apuder/TRS-IO/doc/TRS-IO-M1-labels.png

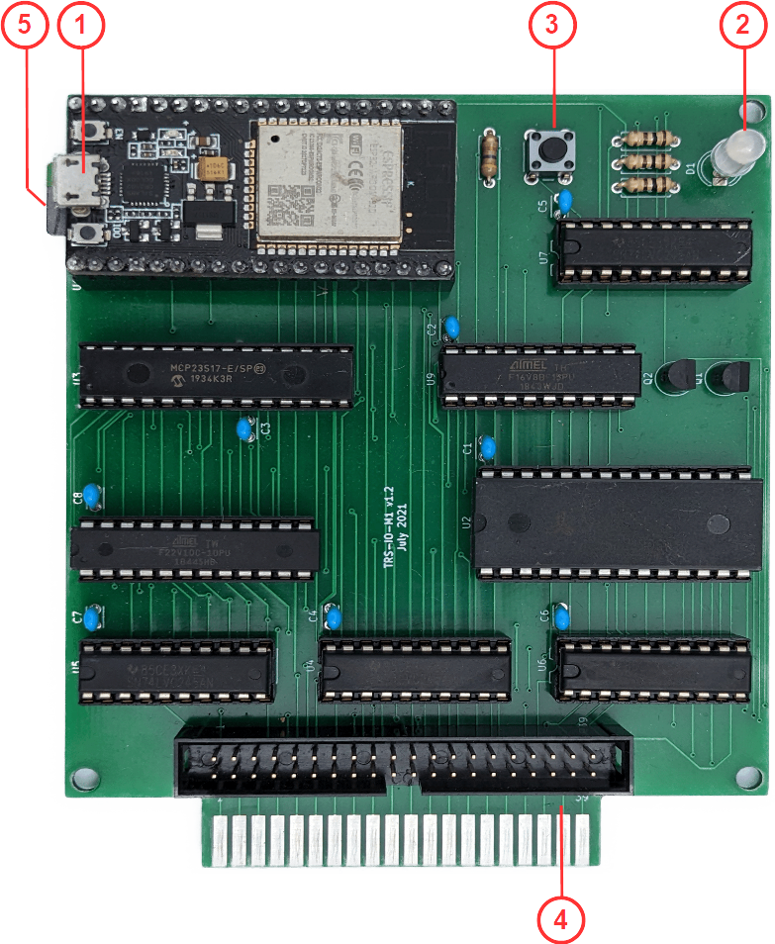
doc/TRS-IO-M1-labels.png
