apuder/TRS-IO/doc/TRS-IO-M1-v1_3.png

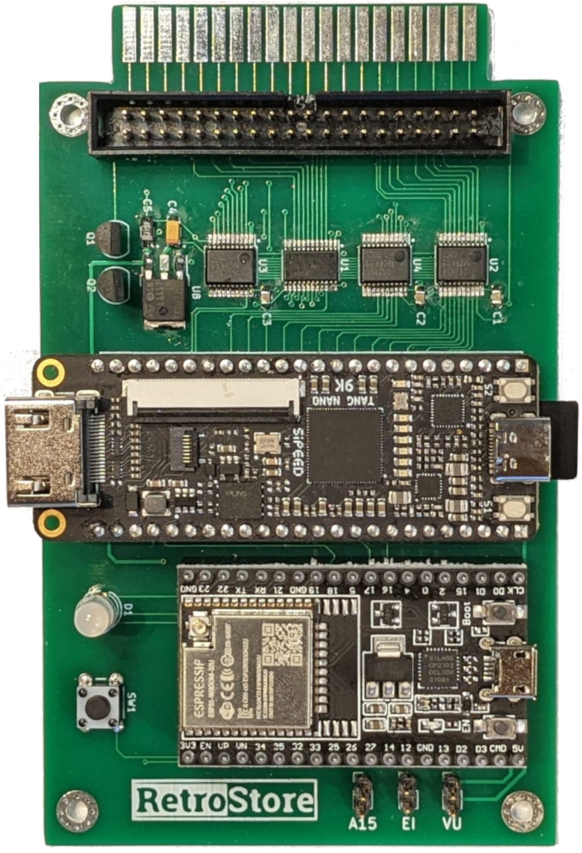
doc/TRS-IO-M1-v1_3.png
