apuder/TRS-IO/doc/TRS-IO-M1-XRAY.png

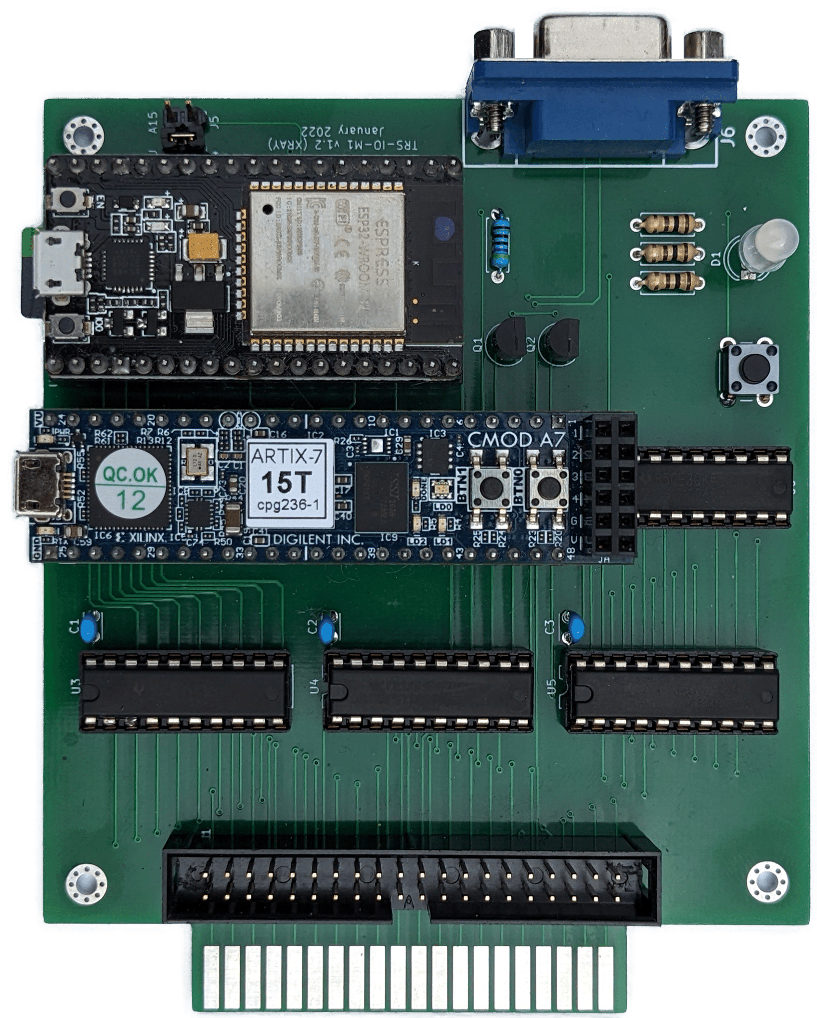
doc/TRS-IO-M1-XRAY.png
