apuder/TRS-IO/doc/TRS-IO-MIII-labels.png

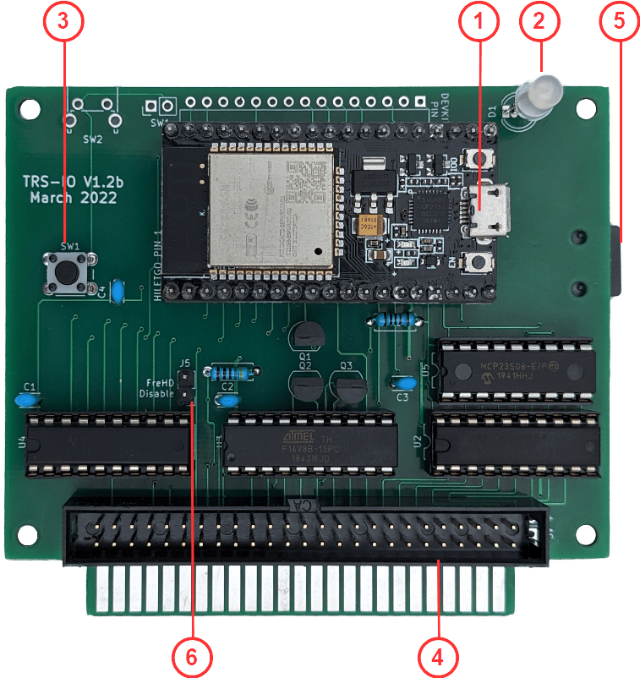
doc/TRS-IO-MIII-labels.png
