apuder/TRS-IO/doc/TRS-IO-MIII.png

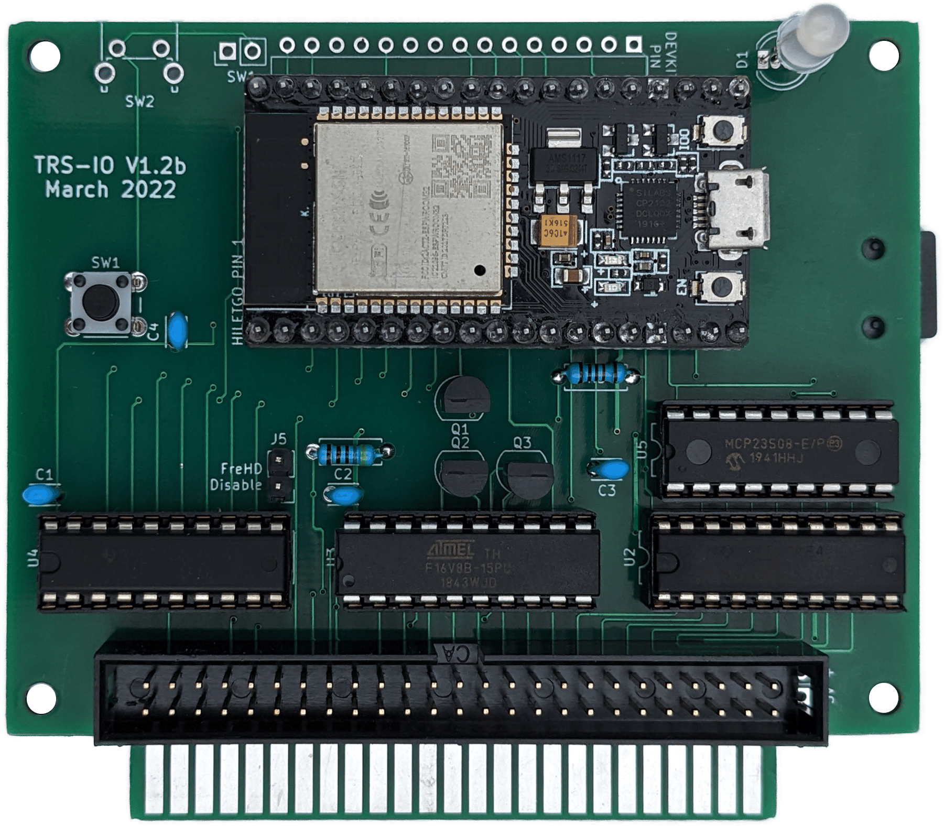
doc/TRS-IO-MIII.png
