apuder/TRS-IO/doc/trs-io-web-ui.png

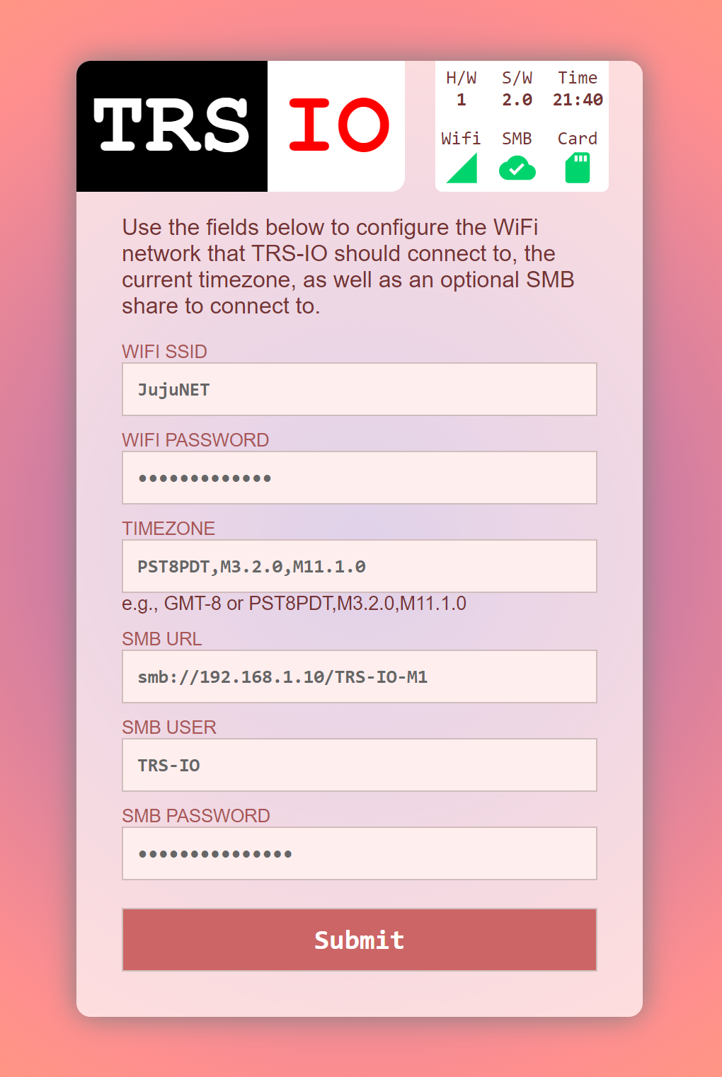
doc/trs-io-web-ui.png
