apuder/TRS-IO/src/images/help-guy.png

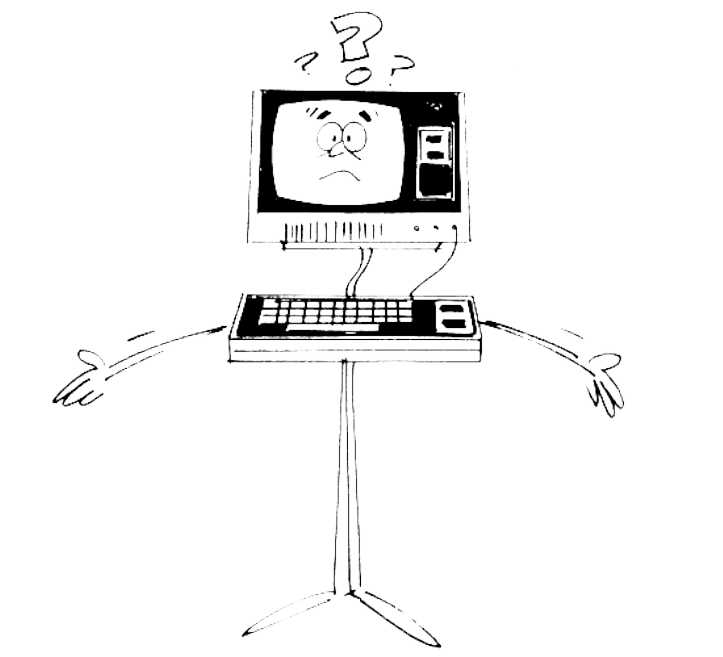
src/images/help-guy.png
