apuder/TRS-IO/src/fpga/pp/v1.1/ptrs-m1/src/gowin_sp/gowin_sp.v

//Copyright (C)2014-2022 Gowin Semiconductor Corporation.
//All rights reserved.
//File Title: IP file
//GOWIN Version: V1.9.8.09 Education
//Part Number: GW2A-LV18PG256C8/I7
//Device: GW2A-18C
//Created Time: Wed Apr 19 12:55:28 2023

module Gowin_SP_RAM (dout, clk, oce, ce, reset, wre, ad, din);

output [7:0] dout;
input clk;
input oce;
input ce;
input reset;
input wre;
input [15:0] ad;
input [7:0] din;

wire [30:0] sp_inst_0_dout_w;
wire [0:0] sp_inst_0_dout;
wire [30:0] sp_inst_1_dout_w;
wire [0:0] sp_inst_1_dout;
wire [30:0] sp_inst_2_dout_w;
wire [0:0] sp_inst_2_dout;
wire [30:0] sp_inst_3_dout_w;
wire [1:1] sp_inst_3_dout;
wire [30:0] sp_inst_4_dout_w;
wire [1:1] sp_inst_4_dout;
wire [30:0] sp_inst_5_dout_w;
wire [1:1] sp_inst_5_dout;
wire [30:0] sp_inst_6_dout_w;
wire [2:2] sp_inst_6_dout;
wire [30:0] sp_inst_7_dout_w;
wire [2:2] sp_inst_7_dout;
wire [30:0] sp_inst_8_dout_w;
wire [2:2] sp_inst_8_dout;
wire [30:0] sp_inst_9_dout_w;
wire [3:3] sp_inst_9_dout;
wire [30:0] sp_inst_10_dout_w;
wire [3:3] sp_inst_10_dout;
wire [30:0] sp_inst_11_dout_w;
wire [3:3] sp_inst_11_dout;
wire [30:0] sp_inst_12_dout_w;
wire [4:4] sp_inst_12_dout;
wire [30:0] sp_inst_13_dout_w;
wire [4:4] sp_inst_13_dout;
wire [30:0] sp_inst_14_dout_w;
wire [4:4] sp_inst_14_dout;
wire [30:0] sp_inst_15_dout_w;
wire [5:5] sp_inst_15_dout;
wire [30:0] sp_inst_16_dout_w;
wire [5:5] sp_inst_16_dout;
wire [30:0] sp_inst_17_dout_w;
wire [5:5] sp_inst_17_dout;
wire [30:0] sp_inst_18_dout_w;
wire [6:6] sp_inst_18_dout;
wire [30:0] sp_inst_19_dout_w;
wire [6:6] sp_inst_19_dout;
wire [30:0] sp_inst_20_dout_w;
wire [6:6] sp_inst_20_dout;
wire [30:0] sp_inst_21_dout_w;
wire [7:7] sp_inst_21_dout;
wire [30:0] sp_inst_22_dout_w;
wire [7:7] sp_inst_22_dout;
wire [30:0] sp_inst_23_dout_w;
wire [7:7] sp_inst_23_dout;
wire dff_q_0;
wire dff_q_1;
wire mux_o_0;
wire mux_o_3;
wire mux_o_6;
wire mux_o_9;
wire mux_o_12;
wire mux_o_15;
wire mux_o_18;
wire mux_o_21;
wire ce_w;
wire gw_gnd;

assign ce_w = ~wre & ce;
assign gw_gnd = 1'b0;

SP sp_inst_0 (
    .DO({sp_inst_0_dout_w[30:0],sp_inst_0_dout[0]}),
    .CLK(clk),
    .OCE(oce),
    .CE(ce),
    .RESET(reset),
    .WRE(wre),
    .BLKSEL({gw_gnd,ad[15],ad[14]}),
    .AD(ad[13:0]),
    .DI({gw_gnd,gw_gnd,gw_gnd,gw_gnd,gw_gnd,gw_gnd,gw_gnd,gw_gnd,gw_gnd,gw_gnd,gw_gnd,gw_gnd,gw_gnd,gw_gnd,gw_gnd,gw_gnd,gw_gnd,gw_gnd,gw_gnd,gw_gnd,gw_gnd,gw_gnd,gw_gnd,gw_gnd,gw_gnd,gw_gnd,gw_gnd,gw_gnd,gw_gnd,gw_gnd,gw_gnd,din[0]})
);

defparam sp_inst_0.READ_MODE = 1'b0;
defparam sp_inst_0.WRITE_MODE = 2'b00;
defparam sp_inst_0.BIT_WIDTH = 1;
defparam sp_inst_0.BLK_SEL = 3'b000;
defparam sp_inst_0.RESET_MODE = "SYNC";
defparam sp_inst_0.INIT_RAM_00 = 256'h0000000000000000000000000000000000000000000000000000000000000000;
defparam sp_inst_0.INIT_RAM_01 = 256'h0000000000000000000000000000000000000000000000000000000000000000;
defparam sp_inst_0.INIT_RAM_02 = 256'h0000000000000000000000000000000000000000000000000000000000000000;
defparam sp_inst_0.INIT_RAM_03 = 256'h0000000000000000000000000000000000000000000000000000000000000000;
defparam sp_inst_0.INIT_RAM_04 = 256'h0000000000000000000000000000000000000000000000000000000000000000;
defparam sp_inst_0.INIT_RAM_05 = 256'h0000000000000000000000000000000000000000000000000000000000000000;
defparam sp_inst_0.INIT_RAM_06 = 256'h0000000000000000000000000000000000000000000000000000000000000000;
defparam sp_inst_0.INIT_RAM_07 = 256'h0000000000000000000000000000000000000000000000000000000000000000;
defparam sp_inst_0.INIT_RAM_08 = 256'h0000000000000000000000000000000000000000000000000000000000000000;
defparam sp_inst_0.INIT_RAM_09 = 256'h0000000000000000000000000000000000000000000000000000000000000000;
defparam sp_inst_0.INIT_RAM_0A = 256'h0000000000000000000000000000000000000000000000000000000000000000;
defparam sp_inst_0.INIT_RAM_0B = 256'h0000000000000000000000000000000000000000000000000000000000000000;
defparam sp_inst_0.INIT_RAM_0C = 256'h0000000000000000000000000000000000000000000000000000000000000000;
defparam sp_inst_0.INIT_RAM_0D = 256'h0000000000000000000000000000000000000000000000000000000000000000;
defparam sp_inst_0.INIT_RAM_0E = 256'h0000000000000000000000000000000000000000000000000000000000000000;
defparam sp_inst_0.INIT_RAM_0F = 256'h0000000000000000000000000000000000000000000000000000000000000000;
defparam sp_inst_0.INIT_RAM_10 = 256'h0000000000000000000000000000000000000000000000000000000000000000;
defparam sp_inst_0.INIT_RAM_11 = 256'h0000000000000000000000000000000000000000000000000000000000000000;
defparam sp_inst_0.INIT_RAM_12 = 256'h0000040000000000000000008000000000000001224ECED4B4DDBABB9CC04820;
defparam sp_inst_0.INIT_RAM_13 = 256'h1008000001C00380000000000000000000000000000000000000000000000000;
defparam sp_inst_0.INIT_RAM_14 = 256'h0000000000000000000000000000000000000000000000000000000E00000000;
defparam sp_inst_0.INIT_RAM_15 = 256'h0000000000000000000000000000000000000000000000000000000000000000;
defparam sp_inst_0.INIT_RAM_16 = 256'h0000000000000000000000000000000000000000000000000000000000000000;
defparam sp_inst_0.INIT_RAM_17 = 256'h0000000000000000000000000000000000000000000000000000000000000000;
defparam sp_inst_0.INIT_RAM_18 = 256'h00000000000000000000000000000000000000000EBF39B3573D5EF44D989997;
defparam sp_inst_0.INIT_RAM_19 = 256'h0000000000000000000000000000000000000000000000000000000000000000;
defparam sp_inst_0.INIT_RAM_1A = 256'h0000000000000000000000000000000000000000000000000000000000000000;
defparam sp_inst_0.INIT_RAM_1B = 256'h0000000000000000000000000000000000000000000000000000000000000000;
defparam sp_inst_0.INIT_RAM_1C = 256'h0000000000000000000000000000000000000000000000000000000000000000;
defparam sp_inst_0.INIT_RAM_1D = 256'h0000000000000000000000000000000000000000000000000000000000000000;
defparam sp_inst_0.INIT_RAM_1E = 256'h0000000000000000000000000000000000000000000000000000000000000000;
defparam sp_inst_0.INIT_RAM_1F = 256'h0000000000000000000000000000000000000000000000000000000000000000;
defparam sp_inst_0.INIT_RAM_20 = 256'h0000000000000000000000000000000000000000000000000000000000000000;
defparam sp_inst_0.INIT_RAM_21 = 256'h0000000000000000000000000000000000000000000000000000000000000000;
defparam sp_inst_0.INIT_RAM_22 = 256'h0000000000000000000000000000000000000000000000000000000000000000;
defparam sp_inst_0.INIT_RAM_23 = 256'h0000000000000000000000000000000000000000000000000000000000000000;
defparam sp_inst_0.INIT_RAM_24 = 256'h0000000000000000000000000000000000000000000000000000000000000000;
defparam sp_inst_0.INIT_RAM_25 = 256'h0000000000000000000000000000000000000000000000000000000000000000;
defparam sp_inst_0.INIT_RAM_26 = 256'h0000000000000000000000000000000000000000000000000000000000000000;
defparam sp_inst_0.INIT_RAM_27 = 256'h0000000000000000000000000000000000000000000000000000000000000000;
defparam sp_inst_0.INIT_RAM_28 = 256'h0000000000000000000000000000000000000000000000000000000000000000;
defparam sp_inst_0.INIT_RAM_29 = 256'h0000000000000000000000000000000000000000000000000000000000000000;
defparam sp_inst_0.INIT_RAM_2A = 256'h0000000000000000000000000000000000000000000000000000000000000000;
defparam sp_inst_0.INIT_RAM_2B = 256'h0000000000000000000000000000000000000000000000000000000000000000;
defparam sp_inst_0.INIT_RAM_2C = 256'h0000000000000000000000000000000000000000000000000000000000000000;
defparam sp_inst_0.INIT_RAM_2D = 256'h0000000000000000000000000000000000000000000000000000000000000000;
defparam sp_inst_0.INIT_RAM_2E = 256'h0000000000000000000000000000000000000000000000000000000000000000;
defparam sp_inst_0.INIT_RAM_2F = 256'h0000000000000000000000000000000000000000000000000000000000000000;
defparam sp_inst_0.INIT_RAM_30 = 256'h0000000000000000000000000000000000000000000000000000000000000000;
defparam sp_inst_0.INIT_RAM_31 = 256'h0000000000000000000000000000000000000000000000000000000000000000;
defparam sp_inst_0.INIT_RAM_32 = 256'h0000000000000000000000000000000000000000000000000000000000000000;
defparam sp_inst_0.INIT_RAM_33 = 256'h0000000000000000000000000000000000000000000000000000000000000000;
defparam sp_inst_0.INIT_RAM_34 = 256'h0000000000000000000000000000000000000000000000000000000000000000;
defparam sp_inst_0.INIT_RAM_35 = 256'h0000000000000000000000000000000000000000000000000000000000000000;
defparam sp_inst_0.INIT_RAM_36 = 256'h0000000000000000000000000000000000000000000000000000000000000000;
defparam sp_inst_0.INIT_RAM_37 = 256'h0000000000000000000000000000000000000000000000000000000000000000;
defparam sp_inst_0.INIT_RAM_38 = 256'h0000000000000000000000000000000000000000000000000000000000000000;
defparam sp_inst_0.INIT_RAM_39 = 256'h0000000000000000000000000000000000000000000000000000000000000000;
defparam sp_inst_0.INIT_RAM_3A = 256'h0000000000000000000000000000000000000000000000000000000000000000;
defparam sp_inst_0.INIT_RAM_3B = 256'h0000000000000000000000000000000000000000000000000000000000000000;
defparam sp_inst_0.INIT_RAM_3C = 256'h0000000000000000000000000000000000000000000000000000000000000000;
defparam sp_inst_0.INIT_RAM_3D = 256'h0000000000000000000000000000000000000000000000000000000000000000;
defparam sp_inst_0.INIT_RAM_3E = 256'h0000000000000000000000000000000000000000000000000000000000000000;
defparam sp_inst_0.INIT_RAM_3F = 256'h0000000000000000000000000000000000000000000000000000000000000000;

SP sp_inst_1 (
    .DO({sp_inst_1_dout_w[30:0],sp_inst_1_dout[0]}),
    .CLK(clk),
    .OCE(oce),
    .CE(ce),
    .RESET(reset),
    .WRE(wre),
    .BLKSEL({gw_gnd,ad[15],ad[14]}),
    .AD(ad[13:0]),
    .DI({gw_gnd,gw_gnd,gw_gnd,gw_gnd,gw_gnd,gw_gnd,gw_gnd,gw_gnd,gw_gnd,gw_gnd,gw_gnd,gw_gnd,gw_gnd,gw_gnd,gw_gnd,gw_gnd,gw_gnd,gw_gnd,gw_gnd,gw_gnd,gw_gnd,gw_gnd,gw_gnd,gw_gnd,gw_gnd,gw_gnd,gw_gnd,gw_gnd,gw_gnd,gw_gnd,gw_gnd,din[0]})
);

defparam sp_inst_1.READ_MODE = 1'b0;
defparam sp_inst_1.WRITE_MODE = 2'b00;
defparam sp_inst_1.BIT_WIDTH = 1;
defparam sp_inst_1.BLK_SEL = 3'b001;
defparam sp_inst_1.RESET_MODE = "SYNC";
defparam sp_inst_1.INIT_RAM_00 = 256'h0000000000000000000000000000000000000000000000000000000000000000;
defparam sp_inst_1.INIT_RAM_01 = 256'h0000000000000000000000000000000000000000000000000000000000000000;
defparam sp_inst_1.INIT_RAM_02 = 256'h0000000000000000000000000000000000000000000000000000000000000000;
defparam sp_inst_1.INIT_RAM_03 = 256'h0000000000000000000000000000000000000000000000000000000000000000;
defparam sp_inst_1.INIT_RAM_04 = 256'h0000000000000000000000000000000000000000000000000000000000000000;
defparam sp_inst_1.INIT_RAM_05 = 256'h0000000000000000000000000000000000000000000000000000000000000000;
defparam sp_inst_1.INIT_RAM_06 = 256'h0000000000000000000000000000000000000000000000000000000000000000;
defparam sp_inst_1.INIT_RAM_07 = 256'h0000000000000000000000000000000000000000000000000000000000000000;
defparam sp_inst_1.INIT_RAM_08 = 256'h0000000000000000000000000000000000000000000000000000000000000000;
defparam sp_inst_1.INIT_RAM_09 = 256'h0000000000000000000000000000000000000000000000000000000000000000;
defparam sp_inst_1.INIT_RAM_0A = 256'h0000000000000000000000000000000000000000000000000000000000000000;
defparam sp_inst_1.INIT_RAM_0B = 256'h0000000000000000000000000000000000000000000000000000000000000000;
defparam sp_inst_1.INIT_RAM_0C = 256'h0000000000000000000000000000000000000000000000000000000000000000;
defparam sp_inst_1.INIT_RAM_0D = 256'h0000000000000000000000000000000000000000000000000000000000000000;
defparam sp_inst_1.INIT_RAM_0E = 256'h0000000000000000000000000000000000000000000000000000000000000000;
defparam sp_inst_1.INIT_RAM_0F = 256'h0000000000000000000000000000000000000000000000000000000000000000;
defparam sp_inst_1.INIT_RAM_10 = 256'h0000000000000000000000000000000000000000000000000000000000000000;
defparam sp_inst_1.INIT_RAM_11 = 256'h0000000000000000000000000000000000000000000000000000000000000000;
defparam sp_inst_1.INIT_RAM_12 = 256'h0000000000000000000000000000000000000000000000000000000000000000;
defparam sp_inst_1.INIT_RAM_13 = 256'h0000000000000000000000000000000000000000000000000000000000000000;
defparam sp_inst_1.INIT_RAM_14 = 256'h0000000000000000000000000000000000000000000000000000000000000000;
defparam sp_inst_1.INIT_RAM_15 = 256'h0000000000000000000000000000000000000000000000000000000000000000;
defparam sp_inst_1.INIT_RAM_16 = 256'h0000000000000000000000000000000000000000000000000000000000000000;
defparam sp_inst_1.INIT_RAM_17 = 256'h0000000000000000000000000000000000000000000000000000000000000000;
defparam sp_inst_1.INIT_RAM_18 = 256'h0000000000000000000000000000000000000000000000000000000000000000;
defparam sp_inst_1.INIT_RAM_19 = 256'h0000000000000000000000000000000000000000000000000000000000000000;
defparam sp_inst_1.INIT_RAM_1A = 256'h0000000000000000000000000000000000000000000000000000000000000000;
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
defparam sp_inst_2.INIT_RAM_35 = 256'h0000000000000000000000000000000000000000000000000000000000000000;
defparam sp_inst_2.INIT_RAM_36 = 256'h0000000000000000000000000000000000000000000000000000000000000000;
defparam sp_inst_2.INIT_RAM_37 = 256'h0000000000000000000000000000000000000000000000000000000000000000;
defparam sp_inst_2.INIT_RAM_38 = 256'h0000000000000000000000000000000000000000000000000000000000000000;
defparam sp_inst_2.INIT_RAM_39 = 256'h0000000000000000000000000000000000000000000000000000000000000000;
defparam sp_inst_2.INIT_RAM_3A = 256'h0000000000000000000000000000000000000000000000000000000000000000;
defparam sp_inst_2.INIT_RAM_3B = 256'h0000000000000000000000000000000000000000000000000000000000000000;
defparam sp_inst_2.INIT_RAM_3C = 256'h0000000000000000000000000000000000000000000000000000000000000000;
defparam sp_inst_2.INIT_RAM_3D = 256'h0000000000000000000000000000000000000000000000000000000000000000;
defparam sp_inst_2.INIT_RAM_3E = 256'h0000000000000000000000000000000000000000000000000000000000000000;
defparam sp_inst_2.INIT_RAM_3F = 256'h0000000000000000000000000000000000000000000000000000000000000000;

SP sp_inst_3 (
    .DO({sp_inst_3_dout_w[30:0],sp_inst_3_dout[1]}),
    .CLK(clk),
    .OCE(oce),
    .CE(ce),
    .RESET(reset),
    .WRE(wre),
    .BLKSEL({gw_gnd,ad[15],ad[14]}),
    .AD(ad[13:0]),
    .DI({gw_gnd,gw_gnd,gw_gnd,gw_gnd,gw_gnd,gw_gnd,gw_gnd,gw_gnd,gw_gnd,gw_gnd,gw_gnd,gw_gnd,gw_gnd,gw_gnd,gw_gnd,gw_gnd,gw_gnd,gw_gnd,gw_gnd,gw_gnd,gw_gnd,gw_gnd,gw_gnd,gw_gnd,gw_gnd,gw_gnd,gw_gnd,gw_gnd,gw_gnd,gw_gnd,gw_gnd,din[1]})
);

defparam sp_inst_3.READ_MODE = 1'b0;
defparam sp_inst_3.WRITE_MODE = 2'b00;
defparam sp_inst_3.BIT_WIDTH = 1;
defparam sp_inst_3.BLK_SEL = 3'b000;
defparam sp_inst_3.RESET_MODE = "SYNC";
defparam sp_inst_3.INIT_RAM_00 = 256'h0000000000000000000000000000000000000000000000000000000000000000;
defparam sp_inst_3.INIT_RAM_01 = 256'h0000000000000000000000000000000000000000000000000000000000000000;
defparam sp_inst_3.INIT_RAM_02 = 256'h0000000000000000000000000000000000000000000000000000000000000000;
defparam sp_inst_3.INIT_RAM_03 = 256'h0000000000000000000000000000000000000000000000000000000000000000;
defparam sp_inst_3.INIT_RAM_04 = 256'h0000000000000000000000000000000000000000000000000000000000000000;
defparam sp_inst_3.INIT_RAM_05 = 256'h0000000000000000000000000000000000000000000000000000000000000000;
defparam sp_inst_3.INIT_RAM_06 = 256'h0000000000000000000000000000000000000000000000000000000000000000;
defparam sp_inst_3.INIT_RAM_07 = 256'h0000000000000000000000000000000000000000000000000000000000000000;
defparam sp_inst_3.INIT_RAM_08 = 256'h0000000000000000000000000000000000000000000000000000000000000000;
defparam sp_inst_3.INIT_RAM_09 = 256'h0000000000000000000000000000000000000000000000000000000000000000;
defparam sp_inst_3.INIT_RAM_0A = 256'h0000000000000000000000000000000000000000000000000000000000000000;
defparam sp_inst_3.INIT_RAM_0B = 256'h0000000000000000000000000000000000000000000000000000000000000000;
defparam sp_inst_3.INIT_RAM_0C = 256'h0000000000000000000000000000000000000000000000000000000000000000;
defparam sp_inst_3.INIT_RAM_0D = 256'h0000000000000000000000000000000000000000000000000000000000000000;
defparam sp_inst_3.INIT_RAM_0E = 256'h0000000000000000000000000000000000000000000000000000000000000000;
defparam sp_inst_3.INIT_RAM_0F = 256'h0000000000000000000000000000000000000000000000000000000000000000;
defparam sp_inst_3.INIT_RAM_10 = 256'h0000000000000000000000000000000000000000000000000000000000000000;
defparam sp_inst_3.INIT_RAM_11 = 256'h0000000000000000000000000000000000000000000000000000000000000000;
defparam sp_inst_3.INIT_RAM_12 = 256'h04040806705CE43BEE700C010082402D822804001202004C3C442E0631A620F7;
defparam sp_inst_3.INIT_RAM_13 = 256'h300BA357262E8C08EB39BE07C00213E48C48E23A360BA31FC5CE8F83F7B9F171;
defparam sp_inst_3.INIT_RAM_14 = 256'h000000000000000000000000000000000000000000000002802223F08A89643C;
defparam sp_inst_3.INIT_RAM_15 = 256'h0000000000000000000000000000000000000000000000000000000000000000;
defparam sp_inst_3.INIT_RAM_16 = 256'h0000000000000000000000000000000000000000000000000000000000000000;
defparam sp_inst_3.INIT_RAM_17 = 256'h0000000000000000000000000000000000000000000000000000000000000000;
defparam sp_inst_3.INIT_RAM_18 = 256'h000000000000000000000000000000000000000000288088C0C62A05682D8000;
defparam sp_inst_3.INIT_RAM_19 = 256'h0000000000000000000000000000000000000000000000000000000000000000;
defparam sp_inst_3.INIT_RAM_1A = 256'h0000000000000000000000000000000000000000000000000000000000000000;
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
defparam sp_inst_4.INIT_RAM_35 = 256'h0000000000000000000000000000000000000000000000000000000000000000;
defparam sp_inst_4.INIT_RAM_36 = 256'h0000000000000000000000000000000000000000000000000000000000000000;
defparam sp_inst_4.INIT_RAM_37 = 256'h0000000000000000000000000000000000000000000000000000000000000000;
defparam sp_inst_4.INIT_RAM_38 = 256'h0000000000000000000000000000000000000000000000000000000000000000;
defparam sp_inst_4.INIT_RAM_39 = 256'h0000000000000000000000000000000000000000000000000000000000000000;
defparam sp_inst_4.INIT_RAM_3A = 256'h0000000000000000000000000000000000000000000000000000000000000000;
defparam sp_inst_4.INIT_RAM_3B = 256'h0000000000000000000000000000000000000000000000000000000000000000;
defparam sp_inst_4.INIT_RAM_3C = 256'h0000000000000000000000000000000000000000000000000000000000000000;
defparam sp_inst_4.INIT_RAM_3D = 256'h0000000000000000000000000000000000000000000000000000000000000000;
defparam sp_inst_4.INIT_RAM_3E = 256'h0000000000000000000000000000000000000000000000000000000000000000;
defparam sp_inst_4.INIT_RAM_3F = 256'h0000000000000000000000000000000000000000000000000000000000000000;

SP sp_inst_5 (
    .DO({sp_inst_5_dout_w[30:0],sp_inst_5_dout[1]}),
    .CLK(clk),
    .OCE(oce),
    .CE(ce),
    .RESET(reset),
    .WRE(wre),
    .BLKSEL({gw_gnd,ad[15],ad[14]}),
    .AD(ad[13:0]),
    .DI({gw_gnd,gw_gnd,gw_gnd,gw_gnd,gw_gnd,gw_gnd,gw_gnd,gw_gnd,gw_gnd,gw_gnd,gw_gnd,gw_gnd,gw_gnd,gw_gnd,gw_gnd,gw_gnd,gw_gnd,gw_gnd,gw_gnd,gw_gnd,gw_gnd,gw_gnd,gw_gnd,gw_gnd,gw_gnd,gw_gnd,gw_gnd,gw_gnd,gw_gnd,gw_gnd,gw_gnd,din[1]})
);

defparam sp_inst_5.READ_MODE = 1'b0;
defparam sp_inst_5.WRITE_MODE = 2'b00;
defparam sp_inst_5.BIT_WIDTH = 1;
defparam sp_inst_5.BLK_SEL = 3'b010;
defparam sp_inst_5.RESET_MODE = "SYNC";
defparam sp_inst_5.INIT_RAM_00 = 256'h0000000000000000000000000000000000000000000000000000000000000000;
defparam sp_inst_5.INIT_RAM_01 = 256'h0000000000000000000000000000000000000000000000000000000000000000;
defparam sp_inst_5.INIT_RAM_02 = 256'h0000000000000000000000000000000000000000000000000000000000000000;
defparam sp_inst_5.INIT_RAM_03 = 256'h0000000000000000000000000000000000000000000000000000000000000000;
defparam sp_inst_5.INIT_RAM_04 = 256'h0000000000000000000000000000000000000000000000000000000000000000;
defparam sp_inst_5.INIT_RAM_05 = 256'h0000000000000000000000000000000000000000000000000000000000000000;
defparam sp_inst_5.INIT_RAM_06 = 256'h0000000000000000000000000000000000000000000000000000000000000000;
defparam sp_inst_5.INIT_RAM_07 = 256'h0000000000000000000000000000000000000000000000000000000000000000;
defparam sp_inst_5.INIT_RAM_08 = 256'h0000000000000000000000000000000000000000000000000000000000000000;
defparam sp_inst_5.INIT_RAM_09 = 256'h0000000000000000000000000000000000000000000000000000000000000000;
defparam sp_inst_5.INIT_RAM_0A = 256'h0000000000000000000000000000000000000000000000000000000000000000;
defparam sp_inst_5.INIT_RAM_0B = 256'h0000000000000000000000000000000000000000000000000000000000000000;
defparam sp_inst_5.INIT_RAM_0C = 256'h0000000000000000000000000000000000000000000000000000000000000000;
defparam sp_inst_5.INIT_RAM_0D = 256'h0000000000000000000000000000000000000000000000000000000000000000;
defparam sp_inst_5.INIT_RAM_0E = 256'h0000000000000000000000000000000000000000000000000000000000000000;
defparam sp_inst_5.INIT_RAM_0F = 256'h0000000000000000000000000000000000000000000000000000000000000000;
defparam sp_inst_5.INIT_RAM_10 = 256'h0000000000000000000000000000000000000000000000000000000000000000;
defparam sp_inst_5.INIT_RAM_11 = 256'h0000000000000000000000000000000000000000000000000000000000000000;
defparam sp_inst_5.INIT_RAM_12 = 256'h0000000000000000000000000000000000000000000000000000000000000000;
defparam sp_inst_5.INIT_RAM_13 = 256'h0000000000000000000000000000000000000000000000000000000000000000;
defparam sp_inst_5.INIT_RAM_14 = 256'h0000000000000000000000000000000000000000000000000000000000000000;
defparam sp_inst_5.INIT_RAM_15 = 256'h0000000000000000000000000000000000000000000000000000000000000000;
defparam sp_inst_5.INIT_RAM_16 = 256'h0000000000000000000000000000000000000000000000000000000000000000;
defparam sp_inst_5.INIT_RAM_17 = 256'h0000000000000000000000000000000000000000000000000000000000000000;
defparam sp_inst_5.INIT_RAM_18 = 256'h0000000000000000000000000000000000000000000000000000000000000000;
defparam sp_inst_5.INIT_RAM_19 = 256'h0000000000000000000000000000000000000000000000000000000000000000;
defparam sp_inst_5.INIT_RAM_1A = 256'h0000000000000000000000000000000000000000000000000000000000000000;
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
defparam sp_inst_6.INIT_RAM_35 = 256'h0000000000000000000000000000000000000000000000000000000000000000;
defparam sp_inst_6.INIT_RAM_36 = 256'h0000000000000000000000000000000000000000000000000000000000000000;
defparam sp_inst_6.INIT_RAM_37 = 256'h0000000000000000000000000000000000000000000000000000000000000000;
defparam sp_inst_6.INIT_RAM_38 = 256'h0000000000000000000000000000000000000000000000000000000000000000;
defparam sp_inst_6.INIT_RAM_39 = 256'h0000000000000000000000000000000000000000000000000000000000000000;
defparam sp_inst_6.INIT_RAM_3A = 256'h0000000000000000000000000000000000000000000000000000000000000000;
defparam sp_inst_6.INIT_RAM_3B = 256'h0000000000000000000000000000000000000000000000000000000000000000;
defparam sp_inst_6.INIT_RAM_3C = 256'h0000000000000000000000000000000000000000000000000000000000000000;
defparam sp_inst_6.INIT_RAM_3D = 256'h0000000000000000000000000000000000000000000000000000000000000000;
defparam sp_inst_6.INIT_RAM_3E = 256'h0000000000000000000000000000000000000000000000000000000000000000;
defparam sp_inst_6.INIT_RAM_3F = 256'h0000000000000000000000000000000000000000000000000000000000000000;

SP sp_inst_7 (
    .DO({sp_inst_7_dout_w[30:0],sp_inst_7_dout[2]}),
    .CLK(clk),
    .OCE(oce),
    .CE(ce),
    .RESET(reset),
    .WRE(wre),
    .BLKSEL({gw_gnd,ad[15],ad[14]}),
    .AD(ad[13:0]),
    .DI({gw_gnd,gw_gnd,gw_gnd,gw_gnd,gw_gnd,gw_gnd,gw_gnd,gw_gnd,gw_gnd,gw_gnd,gw_gnd,gw_gnd,gw_gnd,gw_gnd,gw_gnd,gw_gnd,gw_gnd,gw_gnd,gw_gnd,gw_gnd,gw_gnd,gw_gnd,gw_gnd,gw_gnd,gw_gnd,gw_gnd,gw_gnd,gw_gnd,gw_gnd,gw_gnd,gw_gnd,din[2]})
);

defparam sp_inst_7.READ_MODE = 1'b0;
defparam sp_inst_7.WRITE_MODE = 2'b00;
defparam sp_inst_7.BIT_WIDTH = 1;
defparam sp_inst_7.BLK_SEL = 3'b001;
defparam sp_inst_7.RESET_MODE = "SYNC";
defparam sp_inst_7.INIT_RAM_00 = 256'h0000000000000000000000000000000000000000000000000000000000000000;
defparam sp_inst_7.INIT_RAM_01 = 256'h0000000000000000000000000000000000000000000000000000000000000000;
defparam sp_inst_7.INIT_RAM_02 = 256'h0000000000000000000000000000000000000000000000000000000000000000;
defparam sp_inst_7.INIT_RAM_03 = 256'h0000000000000000000000000000000000000000000000000000000000000000;
defparam sp_inst_7.INIT_RAM_04 = 256'h0000000000000000000000000000000000000000000000000000000000000000;
defparam sp_inst_7.INIT_RAM_05 = 256'h0000000000000000000000000000000000000000000000000000000000000000;
defparam sp_inst_7.INIT_RAM_06 = 256'h0000000000000000000000000000000000000000000000000000000000000000;
defparam sp_inst_7.INIT_RAM_07 = 256'h0000000000000000000000000000000000000000000000000000000000000000;
defparam sp_inst_7.INIT_RAM_08 = 256'h0000000000000000000000000000000000000000000000000000000000000000;
defparam sp_inst_7.INIT_RAM_09 = 256'h0000000000000000000000000000000000000000000000000000000000000000;
defparam sp_inst_7.INIT_RAM_0A = 256'h0000000000000000000000000000000000000000000000000000000000000000;
defparam sp_inst_7.INIT_RAM_0B = 256'h0000000000000000000000000000000000000000000000000000000000000000;
defparam sp_inst_7.INIT_RAM_0C = 256'h0000000000000000000000000000000000000000000000000000000000000000;
defparam sp_inst_7.INIT_RAM_0D = 256'h0000000000000000000000000000000000000000000000000000000000000000;
defparam sp_inst_7.INIT_RAM_0E = 256'h0000000000000000000000000000000000000000000000000000000000000000;
defparam sp_inst_7.INIT_RAM_0F = 256'h0000000000000000000000000000000000000000000000000000000000000000;
defparam sp_inst_7.INIT_RAM_10 = 256'h0000000000000000000000000000000000000000000000000000000000000000;
defparam sp_inst_7.INIT_RAM_11 = 256'h0000000000000000000000000000000000000000000000000000000000000000;
defparam sp_inst_7.INIT_RAM_12 = 256'h0000000000000000000000000000000000000000000000000000000000000000;
defparam sp_inst_7.INIT_RAM_13 = 256'h0000000000000000000000000000000000000000000000000000000000000000;
defparam sp_inst_7.INIT_RAM_14 = 256'h0000000000000000000000000000000000000000000000000000000000000000;
defparam sp_inst_7.INIT_RAM_15 = 256'h0000000000000000000000000000000000000000000000000000000000000000;
defparam sp_inst_7.INIT_RAM_16 = 256'h0000000000000000000000000000000000000000000000000000000000000000;
defparam sp_inst_7.INIT_RAM_17 = 256'h0000000000000000000000000000000000000000000000000000000000000000;
defparam sp_inst_7.INIT_RAM_18 = 256'h0000000000000000000000000000000000000000000000000000000000000000;
defparam sp_inst_7.INIT_RAM_19 = 256'h0000000000000000000000000000000000000000000000000000000000000000;
defparam sp_inst_7.INIT_RAM_1A = 256'h0000000000000000000000000000000000000000000000000000000000000000;
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
defparam sp_inst_8.INIT_RAM_35 = 256'h0000000000000000000000000000000000000000000000000000000000000000;
defparam sp_inst_8.INIT_RAM_36 = 256'h0000000000000000000000000000000000000000000000000000000000000000;
defparam sp_inst_8.INIT_RAM_37 = 256'h0000000000000000000000000000000000000000000000000000000000000000;
defparam sp_inst_8.INIT_RAM_38 = 256'h0000000000000000000000000000000000000000000000000000000000000000;
defparam sp_inst_8.INIT_RAM_39 = 256'h0000000000000000000000000000000000000000000000000000000000000000;
defparam sp_inst_8.INIT_RAM_3A = 256'h0000000000000000000000000000000000000000000000000000000000000000;
defparam sp_inst_8.INIT_RAM_3B = 256'h0000000000000000000000000000000000000000000000000000000000000000;
defparam sp_inst_8.INIT_RAM_3C = 256'h0000000000000000000000000000000000000000000000000000000000000000;
defparam sp_inst_8.INIT_RAM_3D = 256'h0000000000000000000000000000000000000000000000000000000000000000;
defparam sp_inst_8.INIT_RAM_3E = 256'h0000000000000000000000000000000000000000000000000000000000000000;
defparam sp_inst_8.INIT_RAM_3F = 256'h0000000000000000000000000000000000000000000000000000000000000000;

SP sp_inst_9 (
    .DO({sp_inst_9_dout_w[30:0],sp_inst_9_dout[3]}),
    .CLK(clk),
    .OCE(oce),
    .CE(ce),
    .RESET(reset),
    .WRE(wre),
    .BLKSEL({gw_gnd,ad[15],ad[14]}),
    .AD(ad[13:0]),
    .DI({gw_gnd,gw_gnd,gw_gnd,gw_gnd,gw_gnd,gw_gnd,gw_gnd,gw_gnd,gw_gnd,gw_gnd,gw_gnd,gw_gnd,gw_gnd,gw_gnd,gw_gnd,gw_gnd,gw_gnd,gw_gnd,gw_gnd,gw_gnd,gw_gnd,gw_gnd,gw_gnd,gw_gnd,gw_gnd,gw_gnd,gw_gnd,gw_gnd,gw_gnd,gw_gnd,gw_gnd,din[3]})
);

defparam sp_inst_9.READ_MODE = 1'b0;
defparam sp_inst_9.WRITE_MODE = 2'b00;
defparam sp_inst_9.BIT_WIDTH = 1;
defparam sp_inst_9.BLK_SEL = 3'b000;
defparam sp_inst_9.RESET_MODE = "SYNC";
defparam sp_inst_9.INIT_RAM_00 = 256'h0000000000000000000000000000000000000000000000000000000000000000;
defparam sp_inst_9.INIT_RAM_01 = 256'h0000000000000000000000000000000000000000000000000000000000000000;
defparam sp_inst_9.INIT_RAM_02 = 256'h0000000000000000000000000000000000000000000000000000000000000000;
defparam sp_inst_9.INIT_RAM_03 = 256'h0000000000000000000000000000000000000000000000000000000000000000;
defparam sp_inst_9.INIT_RAM_04 = 256'h0000000000000000000000000000000000000000000000000000000000000000;
defparam sp_inst_9.INIT_RAM_05 = 256'h0000000000000000000000000000000000000000000000000000000000000000;
defparam sp_inst_9.INIT_RAM_06 = 256'h0000000000000000000000000000000000000000000000000000000000000000;
defparam sp_inst_9.INIT_RAM_07 = 256'h0000000000000000000000000000000000000000000000000000000000000000;
defparam sp_inst_9.INIT_RAM_08 = 256'h0000000000000000000000000000000000000000000000000000000000000000;
defparam sp_inst_9.INIT_RAM_09 = 256'h0000000000000000000000000000000000000000000000000000000000000000;
defparam sp_inst_9.INIT_RAM_0A = 256'h0000000000000000000000000000000000000000000000000000000000000000;
defparam sp_inst_9.INIT_RAM_0B = 256'h0000000000000000000000000000000000000000000000000000000000000000;
defparam sp_inst_9.INIT_RAM_0C = 256'h0000000000000000000000000000000000000000000000000000000000000000;
defparam sp_inst_9.INIT_RAM_0D = 256'h0000000000000000000000000000000000000000000000000000000000000000;
defparam sp_inst_9.INIT_RAM_0E = 256'h0000000000000000000000000000000000000000000000000000000000000000;
defparam sp_inst_9.INIT_RAM_0F = 256'h0000000000000000000000000000000000000000000000000000000000000000;
defparam sp_inst_9.INIT_RAM_10 = 256'h0000000000000000000000000000000000000000000000000000000000000000;
defparam sp_inst_9.INIT_RAM_11 = 256'h0000000000000000000000000000000000000000000000000000000000000000;
defparam sp_inst_9.INIT_RAM_12 = 256'h11F118D088A30FC02498800311C8102A2A7C04006A68E63247E842889CB380C3;
defparam sp_inst_9.INIT_RAM_13 = 256'h399C63520E048E49F8863E00102A904455551240B50C631096048C4219065FA9;
defparam sp_inst_9.INIT_RAM_14 = 256'h0000000000000000000000000000000000000000000000028042109125631238;
defparam sp_inst_9.INIT_RAM_15 = 256'h0000000000000000000000000000000000000000000000000000000000000000;
defparam sp_inst_9.INIT_RAM_16 = 256'h0000000000000000000000000000000000000000000000000000000000000000;
defparam sp_inst_9.INIT_RAM_17 = 256'h0000000000000000000000000000000000000000000000000000000000000000;
defparam sp_inst_9.INIT_RAM_18 = 256'h00000000000000000000000000000000000000000C7C289957DE5EEDC84780A7;
defparam sp_inst_9.INIT_RAM_19 = 256'h0000000000000000000000000000000000000000000000000000000000000000;
defparam sp_inst_9.INIT_RAM_1A = 256'h0000000000000000000000000000000000000000000000000000000000000000;
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
defparam sp_inst_10.INIT_RAM_34 = 256'h0000000000000000000000000000000000000000000000000000000000000000;
defparam sp_inst_10.INIT_RAM_35 = 256'h0000000000000000000000000000000000000000000000000000000000000000;
defparam sp_inst_10.INIT_RAM_36 = 256'h0000000000000000000000000000000000000000000000000000000000000000;
defparam sp_inst_10.INIT_RAM_37 = 256'h0000000000000000000000000000000000000000000000000000000000000000;
defparam sp_inst_10.INIT_RAM_38 = 256'h0000000000000000000000000000000000000000000000000000000000000000;
defparam sp_inst_10.INIT_RAM_39 = 256'h0000000000000000000000000000000000000000000000000000000000000000;
defparam sp_inst_10.INIT_RAM_3A = 256'h0000000000000000000000000000000000000000000000000000000000000000;
defparam sp_inst_10.INIT_RAM_3B = 256'h0000000000000000000000000000000000000000000000000000000000000000;
defparam sp_inst_10.INIT_RAM_3C = 256'h0000000000000000000000000000000000000000000000000000000000000000;
defparam sp_inst_10.INIT_RAM_3D = 256'h0000000000000000000000000000000000000000000000000000000000000000;
defparam sp_inst_10.INIT_RAM_3E = 256'h0000000000000000000000000000000000000000000000000000000000000000;
defparam sp_inst_10.INIT_RAM_3F = 256'h0000000000000000000000000000000000000000000000000000000000000000;

SP sp_inst_11 (
    .DO({sp_inst_11_dout_w[30:0],sp_inst_11_dout[3]}),
    .CLK(clk),
    .OCE(oce),
    .CE(ce),
    .RESET(reset),
    .WRE(wre),
    .BLKSEL({gw_gnd,ad[15],ad[14]}),
    .AD(ad[13:0]),
    .DI({gw_gnd,gw_gnd,gw_gnd,gw_gnd,gw_gnd,gw_gnd,gw_gnd,gw_gnd,gw_gnd,gw_gnd,gw_gnd,gw_gnd,gw_gnd,gw_gnd,gw_gnd,gw_gnd,gw_gnd,gw_gnd,gw_gnd,gw_gnd,gw_gnd,gw_gnd,gw_gnd,gw_gnd,gw_gnd,gw_gnd,gw_gnd,gw_gnd,gw_gnd,gw_gnd,gw_gnd,din[3]})
);

defparam sp_inst_11.READ_MODE = 1'b0;
defparam sp_inst_11.WRITE_MODE = 2'b00;
defparam sp_inst_11.BIT_WIDTH = 1;
defparam sp_inst_11.BLK_SEL = 3'b010;
defparam sp_inst_11.RESET_MODE = "SYNC";
defparam sp_inst_11.INIT_RAM_00 = 256'h0000000000000000000000000000000000000000000000000000000000000000;
defparam sp_inst_11.INIT_RAM_01 = 256'h0000000000000000000000000000000000000000000000000000000000000000;
defparam sp_inst_11.INIT_RAM_02 = 256'h0000000000000000000000000000000000000000000000000000000000000000;
defparam sp_inst_11.INIT_RAM_03 = 256'h0000000000000000000000000000000000000000000000000000000000000000;
defparam sp_inst_11.INIT_RAM_04 = 256'h0000000000000000000000000000000000000000000000000000000000000000;
defparam sp_inst_11.INIT_RAM_05 = 256'h0000000000000000000000000000000000000000000000000000000000000000;
defparam sp_inst_11.INIT_RAM_06 = 256'h0000000000000000000000000000000000000000000000000000000000000000;
defparam sp_inst_11.INIT_RAM_07 = 256'h0000000000000000000000000000000000000000000000000000000000000000;
defparam sp_inst_11.INIT_RAM_08 = 256'h0000000000000000000000000000000000000000000000000000000000000000;
defparam sp_inst_11.INIT_RAM_09 = 256'h0000000000000000000000000000000000000000000000000000000000000000;
defparam sp_inst_11.INIT_RAM_0A = 256'h0000000000000000000000000000000000000000000000000000000000000000;
defparam sp_inst_11.INIT_RAM_0B = 256'h0000000000000000000000000000000000000000000000000000000000000000;
defparam sp_inst_11.INIT_RAM_0C = 256'h0000000000000000000000000000000000000000000000000000000000000000;
defparam sp_inst_11.INIT_RAM_0D = 256'h0000000000000000000000000000000000000000000000000000000000000000;
defparam sp_inst_11.INIT_RAM_0E = 256'h0000000000000000000000000000000000000000000000000000000000000000;
defparam sp_inst_11.INIT_RAM_0F = 256'h0000000000000000000000000000000000000000000000000000000000000000;
defparam sp_inst_11.INIT_RAM_10 = 256'h0000000000000000000000000000000000000000000000000000000000000000;
defparam sp_inst_11.INIT_RAM_11 = 256'h0000000000000000000000000000000000000000000000000000000000000000;
defparam sp_inst_11.INIT_RAM_12 = 256'h0000000000000000000000000000000000000000000000000000000000000000;
defparam sp_inst_11.INIT_RAM_13 = 256'h0000000000000000000000000000000000000000000000000000000000000000;
defparam sp_inst_11.INIT_RAM_14 = 256'h0000000000000000000000000000000000000000000000000000000000000000;
defparam sp_inst_11.INIT_RAM_15 = 256'h0000000000000000000000000000000000000000000000000000000000000000;
defparam sp_inst_11.INIT_RAM_16 = 256'h0000000000000000000000000000000000000000000000000000000000000000;
defparam sp_inst_11.INIT_RAM_17 = 256'h0000000000000000000000000000000000000000000000000000000000000000;
defparam sp_inst_11.INIT_RAM_18 = 256'h0000000000000000000000000000000000000000000000000000000000000000;
defparam sp_inst_11.INIT_RAM_19 = 256'h0000000000000000000000000000000000000000000000000000000000000000;
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
    .BLKSEL({gw_gnd,ad[15],ad[14]}),
    .AD(ad[13:0]),
    .DI({gw_gnd,gw_gnd,gw_gnd,gw_gnd,gw_gnd,gw_gnd,gw_gnd,gw_gnd,gw_gnd,gw_gnd,gw_gnd,gw_gnd,gw_gnd,gw_gnd,gw_gnd,gw_gnd,gw_gnd,gw_gnd,gw_gnd,gw_gnd,gw_gnd,gw_gnd,gw_gnd,gw_gnd,gw_gnd,gw_gnd,gw_gnd,gw_gnd,gw_gnd,gw_gnd,gw_gnd,din[4]})
);

defparam sp_inst_12.READ_MODE = 1'b0;
defparam sp_inst_12.WRITE_MODE = 2'b00;
defparam sp_inst_12.BIT_WIDTH = 1;
defparam sp_inst_12.BLK_SEL = 3'b000;
defparam sp_inst_12.RESET_MODE = "SYNC";
defparam sp_inst_12.INIT_RAM_00 = 256'h0000000000000000000000000000000000000000000000000000000000000000;
defparam sp_inst_12.INIT_RAM_01 = 256'h0000000000000000000000000000000000000000000000000000000000000000;
defparam sp_inst_12.INIT_RAM_02 = 256'h0000000000000000000000000000000000000000000000000000000000000000;
defparam sp_inst_12.INIT_RAM_03 = 256'h0000000000000000000000000000000000000000000000000000000000000000;
defparam sp_inst_12.INIT_RAM_04 = 256'h0000000000000000000000000000000000000000000000000000000000000000;
defparam sp_inst_12.INIT_RAM_05 = 256'h0000000000000000000000000000000000000000000000000000000000000000;
defparam sp_inst_12.INIT_RAM_06 = 256'h0000000000000000000000000000000000000000000000000000000000000000;
defparam sp_inst_12.INIT_RAM_07 = 256'h0000000000000000000000000000000000000000000000000000000000000000;
defparam sp_inst_12.INIT_RAM_08 = 256'h0000000000000000000000000000000000000000000000000000000000000000;
defparam sp_inst_12.INIT_RAM_09 = 256'h0000000000000000000000000000000000000000000000000000000000000000;
defparam sp_inst_12.INIT_RAM_0A = 256'h0000000000000000000000000000000000000000000000000000000000000000;
defparam sp_inst_12.INIT_RAM_0B = 256'h0000000000000000000000000000000000000000000000000000000000000000;
defparam sp_inst_12.INIT_RAM_0C = 256'h0000000000000000000000000000000000000000000000000000000000000000;
defparam sp_inst_12.INIT_RAM_0D = 256'h0000000000000000000000000000000000000000000000000000000000000000;
defparam sp_inst_12.INIT_RAM_0E = 256'h0000000000000000000000000000000000000000000000000000000000000000;
defparam sp_inst_12.INIT_RAM_0F = 256'h0000000000000000000000000000000000000000000000000000000000000000;
defparam sp_inst_12.INIT_RAM_10 = 256'h0000000000000000000000000000000000000000000000000000000000000000;
defparam sp_inst_12.INIT_RAM_11 = 256'h0000000000000000000000000000000000000000000000000000000000000000;
defparam sp_inst_12.INIT_RAM_12 = 256'h2000801E711F04B1C4A901F07FE8104447280400C10A66E2D9684D040037F0C3;
defparam sp_inst_12.INIT_RAM_13 = 256'h799C675216049E5D1CC670403FF2108424551239F17C73508E04FE4E7905D1B2;
defparam sp_inst_12.INIT_RAM_14 = 256'h0000000000000000000000000000000000000000000000054080091154631206;
defparam sp_inst_12.INIT_RAM_15 = 256'h0000000000000000000000000000000000000000000000000000000000000000;
defparam sp_inst_12.INIT_RAM_16 = 256'h0000000000000000000000000000000000000000000000000000000000000000;
defparam sp_inst_12.INIT_RAM_17 = 256'h0000000000000000000000000000000000000000000000000000000000000000;
defparam sp_inst_12.INIT_RAM_18 = 256'h000000000000000000000000000000000000000006DC19482DDE95FDD81C10AF;
defparam sp_inst_12.INIT_RAM_19 = 256'h0000000000000000000000000000000000000000000000000000000000000000;
defparam sp_inst_12.INIT_RAM_1A = 256'h0000000000000000000000000000000000000000000000000000000000000000;
defparam sp_inst_12.INIT_RAM_1B = 256'h0000000000000000000000000000000000000000000000000000000000000000;
defparam sp_inst_12.INIT_RAM_1C = 256'h0000000000000000000000000000000000000000000000000000000000000000;
defparam sp_inst_12.INIT_RAM_1D = 256'h0000000000000000000000000000000000000000000000000000000000000000;
defparam sp_inst_12.INIT_RAM_1E = 256'h0000000000000000000000000000000000000000000000000000000000000000;
defparam sp_inst_12.INIT_RAM_1F = 256'h0000000000000000000000000000000000000000000000000000000000000000;
defparam sp_inst_12.INIT_RAM_20 = 256'h0000000000000000000000000000000000000000000000000000000000000000;
defparam sp_inst_12.INIT_RAM_21 = 256'h0000000000000000000000000000000000000000000000000000000000000000;
defparam sp_inst_12.INIT_RAM_22 = 256'h0000000000000000000000000000000000000000000000000000000000000000;
defparam sp_inst_12.INIT_RAM_23 = 256'h0000000000000000000000000000000000000000000000000000000000000000;
defparam sp_inst_12.INIT_RAM_24 = 256'h0000000000000000000000000000000000000000000000000000000000000000;
defparam sp_inst_12.INIT_RAM_25 = 256'h0000000000000000000000000000000000000000000000000000000000000000;
defparam sp_inst_12.INIT_RAM_26 = 256'h0000000000000000000000000000000000000000000000000000000000000000;
defparam sp_inst_12.INIT_RAM_27 = 256'h0000000000000000000000000000000000000000000000000000000000000000;
defparam sp_inst_12.INIT_RAM_28 = 256'h0000000000000000000000000000000000000000000000000000000000000000;
defparam sp_inst_12.INIT_RAM_29 = 256'h0000000000000000000000000000000000000000000000000000000000000000;
defparam sp_inst_12.INIT_RAM_2A = 256'h0000000000000000000000000000000000000000000000000000000000000000;
defparam sp_inst_12.INIT_RAM_2B = 256'h0000000000000000000000000000000000000000000000000000000000000000;
defparam sp_inst_12.INIT_RAM_2C = 256'h0000000000000000000000000000000000000000000000000000000000000000;
defparam sp_inst_12.INIT_RAM_2D = 256'h0000000000000000000000000000000000000000000000000000000000000000;
defparam sp_inst_12.INIT_RAM_2E = 256'h0000000000000000000000000000000000000000000000000000000000000000;
defparam sp_inst_12.INIT_RAM_2F = 256'h0000000000000000000000000000000000000000000000000000000000000000;
defparam sp_inst_12.INIT_RAM_30 = 256'h0000000000000000000000000000000000000000000000000000000000000000;
defparam sp_inst_12.INIT_RAM_31 = 256'h0000000000000000000000000000000000000000000000000000000000000000;
defparam sp_inst_12.INIT_RAM_32 = 256'h0000000000000000000000000000000000000000000000000000000000000000;
defparam sp_inst_12.INIT_RAM_33 = 256'h0000000000000000000000000000000000000000000000000000000000000000;
defparam sp_inst_12.INIT_RAM_34 = 256'h0000000000000000000000000000000000000000000000000000000000000000;
defparam sp_inst_12.INIT_RAM_35 = 256'h0000000000000000000000000000000000000000000000000000000000000000;
defparam sp_inst_12.INIT_RAM_36 = 256'h0000000000000000000000000000000000000000000000000000000000000000;
defparam sp_inst_12.INIT_RAM_37 = 256'h0000000000000000000000000000000000000000000000000000000000000000;
defparam sp_inst_12.INIT_RAM_38 = 256'h0000000000000000000000000000000000000000000000000000000000000000;
defparam sp_inst_12.INIT_RAM_39 = 256'h0000000000000000000000000000000000000000000000000000000000000000;
defparam sp_inst_12.INIT_RAM_3A = 256'h0000000000000000000000000000000000000000000000000000000000000000;
defparam sp_inst_12.INIT_RAM_3B = 256'h0000000000000000000000000000000000000000000000000000000000000000;
defparam sp_inst_12.INIT_RAM_3C = 256'h0000000000000000000000000000000000000000000000000000000000000000;
defparam sp_inst_12.INIT_RAM_3D = 256'h0000000000000000000000000000000000000000000000000000000000000000;
defparam sp_inst_12.INIT_RAM_3E = 256'h0000000000000000000000000000000000000000000000000000000000000000;
defparam sp_inst_12.INIT_RAM_3F = 256'h0000000000000000000000000000000000000000000000000000000000000000;

SP sp_inst_13 (
    .DO({sp_inst_13_dout_w[30:0],sp_inst_13_dout[4]}),
    .CLK(clk),
    .OCE(oce),
    .CE(ce),
    .RESET(reset),
    .WRE(wre),
    .BLKSEL({gw_gnd,ad[15],ad[14]}),
    .AD(ad[13:0]),
    .DI({gw_gnd,gw_gnd,gw_gnd,gw_gnd,gw_gnd,gw_gnd,gw_gnd,gw_gnd,gw_gnd,gw_gnd,gw_gnd,gw_gnd,gw_gnd,gw_gnd,gw_gnd,gw_gnd,gw_gnd,gw_gnd,gw_gnd,gw_gnd,gw_gnd,gw_gnd,gw_gnd,gw_gnd,gw_gnd,gw_gnd,gw_gnd,gw_gnd,gw_gnd,gw_gnd,gw_gnd,din[4]})
);

defparam sp_inst_13.READ_MODE = 1'b0;
defparam sp_inst_13.WRITE_MODE = 2'b00;
defparam sp_inst_13.BIT_WIDTH = 1;
defparam sp_inst_13.BLK_SEL = 3'b001;
defparam sp_inst_13.RESET_MODE = "SYNC";
defparam sp_inst_13.INIT_RAM_00 = 256'h0000000000000000000000000000000000000000000000000000000000000000;
defparam sp_inst_13.INIT_RAM_01 = 256'h0000000000000000000000000000000000000000000000000000000000000000;
defparam sp_inst_13.INIT_RAM_02 = 256'h0000000000000000000000000000000000000000000000000000000000000000;
defparam sp_inst_13.INIT_RAM_03 = 256'h0000000000000000000000000000000000000000000000000000000000000000;
defparam sp_inst_13.INIT_RAM_04 = 256'h0000000000000000000000000000000000000000000000000000000000000000;
defparam sp_inst_13.INIT_RAM_05 = 256'h0000000000000000000000000000000000000000000000000000000000000000;
defparam sp_inst_13.INIT_RAM_06 = 256'h0000000000000000000000000000000000000000000000000000000000000000;
defparam sp_inst_13.INIT_RAM_07 = 256'h0000000000000000000000000000000000000000000000000000000000000000;
defparam sp_inst_13.INIT_RAM_08 = 256'h0000000000000000000000000000000000000000000000000000000000000000;
defparam sp_inst_13.INIT_RAM_09 = 256'h0000000000000000000000000000000000000000000000000000000000000000;
defparam sp_inst_13.INIT_RAM_0A = 256'h0000000000000000000000000000000000000000000000000000000000000000;
defparam sp_inst_13.INIT_RAM_0B = 256'h0000000000000000000000000000000000000000000000000000000000000000;
defparam sp_inst_13.INIT_RAM_0C = 256'h0000000000000000000000000000000000000000000000000000000000000000;
defparam sp_inst_13.INIT_RAM_0D = 256'h0000000000000000000000000000000000000000000000000000000000000000;
defparam sp_inst_13.INIT_RAM_0E = 256'h0000000000000000000000000000000000000000000000000000000000000000;
defparam sp_inst_13.INIT_RAM_0F = 256'h0000000000000000000000000000000000000000000000000000000000000000;
defparam sp_inst_13.INIT_RAM_10 = 256'h0000000000000000000000000000000000000000000000000000000000000000;
defparam sp_inst_13.INIT_RAM_11 = 256'h0000000000000000000000000000000000000000000000000000000000000000;
defparam sp_inst_13.INIT_RAM_12 = 256'h0000000000000000000000000000000000000000000000000000000000000000;
defparam sp_inst_13.INIT_RAM_13 = 256'h0000000000000000000000000000000000000000000000000000000000000000;
defparam sp_inst_13.INIT_RAM_14 = 256'h0000000000000000000000000000000000000000000000000000000000000000;
defparam sp_inst_13.INIT_RAM_15 = 256'h0000000000000000000000000000000000000000000000000000000000000000;
defparam sp_inst_13.INIT_RAM_16 = 256'h0000000000000000000000000000000000000000000000000000000000000000;
defparam sp_inst_13.INIT_RAM_17 = 256'h0000000000000000000000000000000000000000000000000000000000000000;
defparam sp_inst_13.INIT_RAM_18 = 256'h0000000000000000000000000000000000000000000000000000000000000000;
defparam sp_inst_13.INIT_RAM_19 = 256'h0000000000000000000000000000000000000000000000000000000000000000;
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
defparam sp_inst_14.INIT_RAM_34 = 256'h0000000000000000000000000000000000000000000000000000000000000000;
defparam sp_inst_14.INIT_RAM_35 = 256'h0000000000000000000000000000000000000000000000000000000000000000;
defparam sp_inst_14.INIT_RAM_36 = 256'h0000000000000000000000000000000000000000000000000000000000000000;
defparam sp_inst_14.INIT_RAM_37 = 256'h0000000000000000000000000000000000000000000000000000000000000000;
defparam sp_inst_14.INIT_RAM_38 = 256'h0000000000000000000000000000000000000000000000000000000000000000;
defparam sp_inst_14.INIT_RAM_39 = 256'h0000000000000000000000000000000000000000000000000000000000000000;
defparam sp_inst_14.INIT_RAM_3A = 256'h0000000000000000000000000000000000000000000000000000000000000000;
defparam sp_inst_14.INIT_RAM_3B = 256'h0000000000000000000000000000000000000000000000000000000000000000;
defparam sp_inst_14.INIT_RAM_3C = 256'h0000000000000000000000000000000000000000000000000000000000000000;
defparam sp_inst_14.INIT_RAM_3D = 256'h0000000000000000000000000000000000000000000000000000000000000000;
defparam sp_inst_14.INIT_RAM_3E = 256'h0000000000000000000000000000000000000000000000000000000000000000;
defparam sp_inst_14.INIT_RAM_3F = 256'h0000000000000000000000000000000000000000000000000000000000000000;

SP sp_inst_15 (
    .DO({sp_inst_15_dout_w[30:0],sp_inst_15_dout[5]}),
    .CLK(clk),
    .OCE(oce),
    .CE(ce),
    .RESET(reset),
    .WRE(wre),
    .BLKSEL({gw_gnd,ad[15],ad[14]}),
    .AD(ad[13:0]),
    .DI({gw_gnd,gw_gnd,gw_gnd,gw_gnd,gw_gnd,gw_gnd,gw_gnd,gw_gnd,gw_gnd,gw_gnd,gw_gnd,gw_gnd,gw_gnd,gw_gnd,gw_gnd,gw_gnd,gw_gnd,gw_gnd,gw_gnd,gw_gnd,gw_gnd,gw_gnd,gw_gnd,gw_gnd,gw_gnd,gw_gnd,gw_gnd,gw_gnd,gw_gnd,gw_gnd,gw_gnd,din[5]})
);

defparam sp_inst_15.READ_MODE = 1'b0;
defparam sp_inst_15.WRITE_MODE = 2'b00;
defparam sp_inst_15.BIT_WIDTH = 1;
defparam sp_inst_15.BLK_SEL = 3'b000;
defparam sp_inst_15.RESET_MODE = "SYNC";
defparam sp_inst_15.INIT_RAM_00 = 256'h0000000000000000000000000000000000000000000000000000000000000000;
defparam sp_inst_15.INIT_RAM_01 = 256'h0000000000000000000000000000000000000000000000000000000000000000;
defparam sp_inst_15.INIT_RAM_02 = 256'h0000000000000000000000000000000000000000000000000000000000000000;
defparam sp_inst_15.INIT_RAM_03 = 256'h0000000000000000000000000000000000000000000000000000000000000000;
defparam sp_inst_15.INIT_RAM_04 = 256'h0000000000000000000000000000000000000000000000000000000000000000;
defparam sp_inst_15.INIT_RAM_05 = 256'h0000000000000000000000000000000000000000000000000000000000000000;
defparam sp_inst_15.INIT_RAM_06 = 256'h0000000000000000000000000000000000000000000000000000000000000000;
defparam sp_inst_15.INIT_RAM_07 = 256'h0000000000000000000000000000000000000000000000000000000000000000;
defparam sp_inst_15.INIT_RAM_08 = 256'h0000000000000000000000000000000000000000000000000000000000000000;
defparam sp_inst_15.INIT_RAM_09 = 256'h0000000000000000000000000000000000000000000000000000000000000000;
defparam sp_inst_15.INIT_RAM_0A = 256'h0000000000000000000000000000000000000000000000000000000000000000;
defparam sp_inst_15.INIT_RAM_0B = 256'h0000000000000000000000000000000000000000000000000000000000000000;
defparam sp_inst_15.INIT_RAM_0C = 256'h0000000000000000000000000000000000000000000000000000000000000000;
defparam sp_inst_15.INIT_RAM_0D = 256'h0000000000000000000000000000000000000000000000000000000000000000;
defparam sp_inst_15.INIT_RAM_0E = 256'h0000000000000000000000000000000000000000000000000000000000000000;
defparam sp_inst_15.INIT_RAM_0F = 256'h0000000000000000000000000000000000000000000000000000000000000000;
defparam sp_inst_15.INIT_RAM_10 = 256'h0000000000000000000000000000000000000000000000000000000000000000;
defparam sp_inst_15.INIT_RAM_11 = 256'h0000000000000000000000000000000000000000000000000000000000000000;
defparam sp_inst_15.INIT_RAM_12 = 256'h11F118D18A02F54204CA000011C8108A82FD4403E7FD88CFE567B3820DDA09EF;
defparam sp_inst_15.INIT_RAM_13 = 256'hB66B9AB226066D88EB39AE201022550A54631206318C6B509604884219065184;
defparam sp_inst_15.INIT_RAM_14 = 256'h000000000000000000000000000000000000000000000002904213F18C631FF9;
defparam sp_inst_15.INIT_RAM_15 = 256'h0000000000000000000000000000000000000000000000000000000000000000;
defparam sp_inst_15.INIT_RAM_16 = 256'h0000000000000000000000000000000000000000000000000000000000000000;
defparam sp_inst_15.INIT_RAM_17 = 256'h0000000000000000000000000000000000000000000000000000000000000000;
defparam sp_inst_15.INIT_RAM_18 = 256'h00000000000000000000000000000000000000000BCE4000F2F7EA0DB0008010;
defparam sp_inst_15.INIT_RAM_19 = 256'h0000000000000000000000000000000000000000000000000000000000000000;
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
    .BLKSEL({gw_gnd,ad[15],ad[14]}),
    .AD(ad[13:0]),
    .DI({gw_gnd,gw_gnd,gw_gnd,gw_gnd,gw_gnd,gw_gnd,gw_gnd,gw_gnd,gw_gnd,gw_gnd,gw_gnd,gw_gnd,gw_gnd,gw_gnd,gw_gnd,gw_gnd,gw_gnd,gw_gnd,gw_gnd,gw_gnd,gw_gnd,gw_gnd,gw_gnd,gw_gnd,gw_gnd,gw_gnd,gw_gnd,gw_gnd,gw_gnd,gw_gnd,gw_gnd,din[5]})
);
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
